zaccowan/Project-ZigBee/zigbee_schematics/zigbee.kicad_sch

## KiCad design zigbee_schematics/zigbee.kicad_sch (2024-04-29)

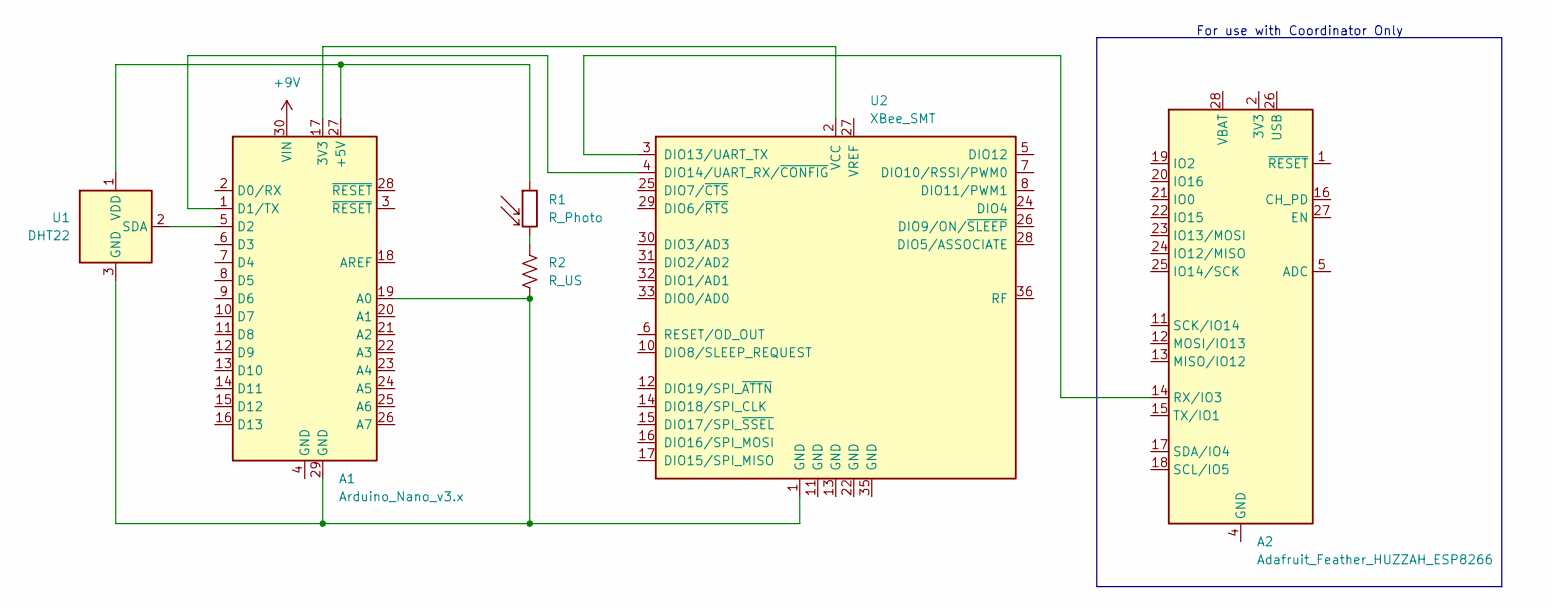
[picture p4: schematic zigbee.kicad_sch]

Parts:
A1: Arduino_Nano_v3.x; Arduino_Nano
A2: Adafruit_Feather_HUZZAH_ESP8266; Adafruit_Feather
R1: R_Photo
R2: R_US
U1: DHT22; ASAIR_AM2302_P2.54mm_Vertical
U2: XBee_SMT; Digi_XBee_SMT

Connections:
+9V: A1.30 (VIN)
unnamed: A1.1 (D1/TX), U2.4 (DIO14/UART_RX/~CONFIG)
unnamed: A1.5 (D2), U1.2 (SDA)
unnamed: A1.17 (3V3), U2.2 (VCC)
unnamed: A1.19 (A0), A1.29 (GND), R2.2, U1.3 (GND), U1.4 (GND), U2.1 (GND)
unnamed: A1.27 (+5V), R1.1, U1.1 (VDD)
unnamed: A2.14 (RX/IO3), U2.3 (DIO13/UART_TX)
unnamed: R1.2, R2.1

Notes on the sheet:
For use with Coordinator Only
